ObiKwiet/Ultralight-Headset/Drawings/SCH1100-2 - IO Module r-.pdf

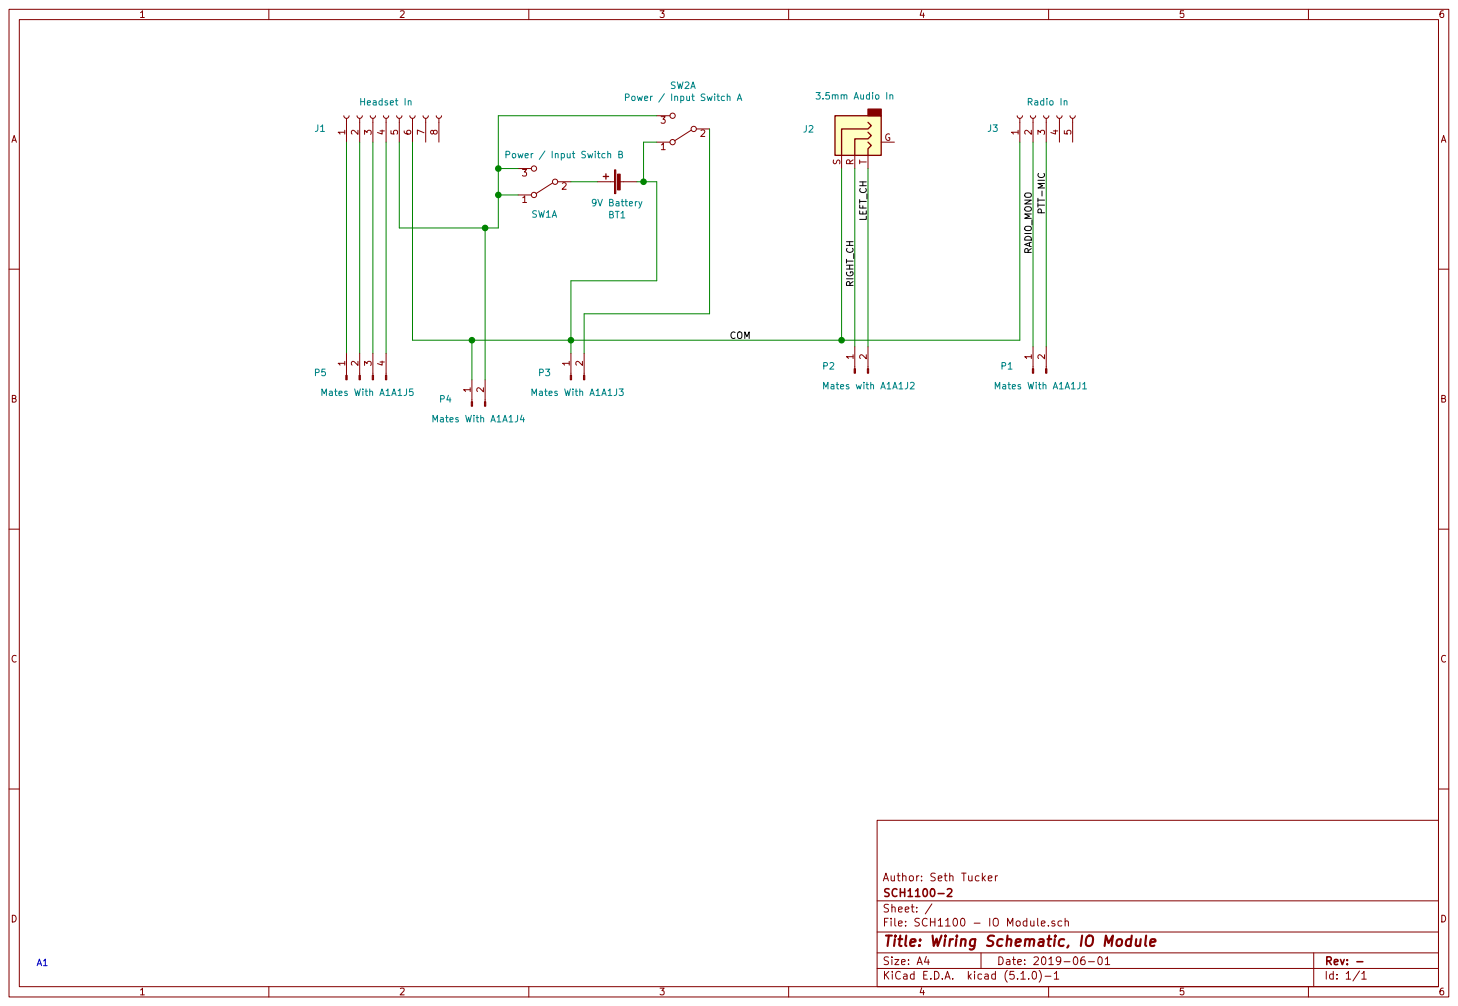
[picture p18: page 1]

Power / Input Switch A COM

File: SCH1100 - IO Module.sch Sheet: / SCH1100-2 Author: Seth Tucker

Id: 1/1 Title: Wiring Schematic, IO Module
