ObiKwiet/Ultralight-Headset/Drawings/SCH1110-2 - IO Module PCB r-.pdf

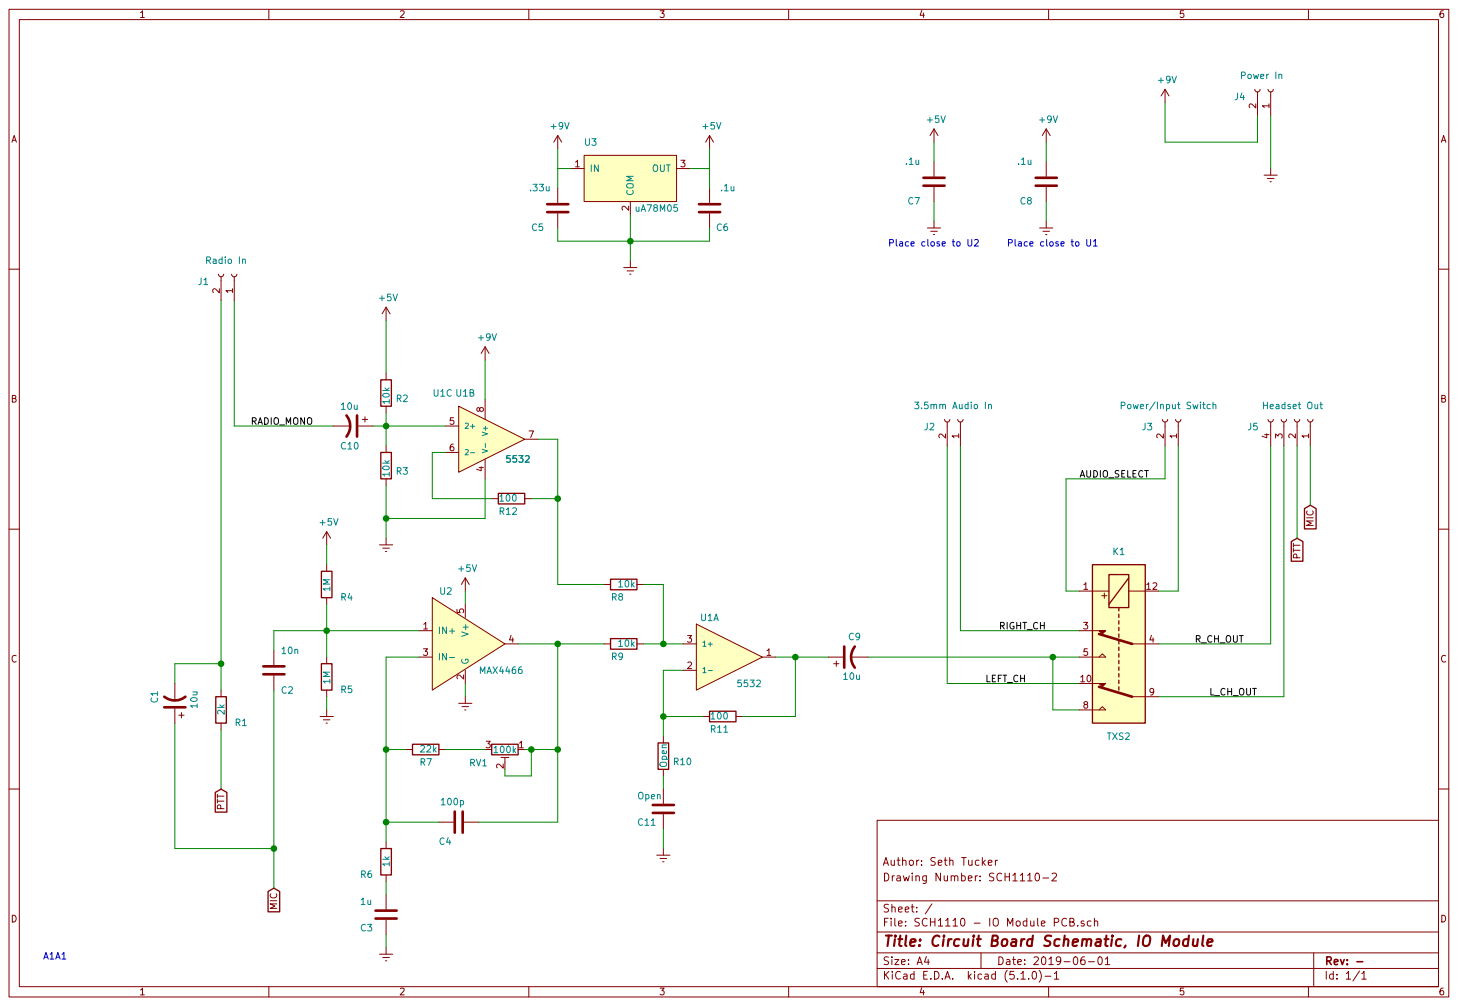
[picture p19: page 1]

Id: 1/1 Title: Circuit Board Schematic, IO Module
