ObiKwiet/Ultralight-Headset/Drawings/Drawing Tree.pdf

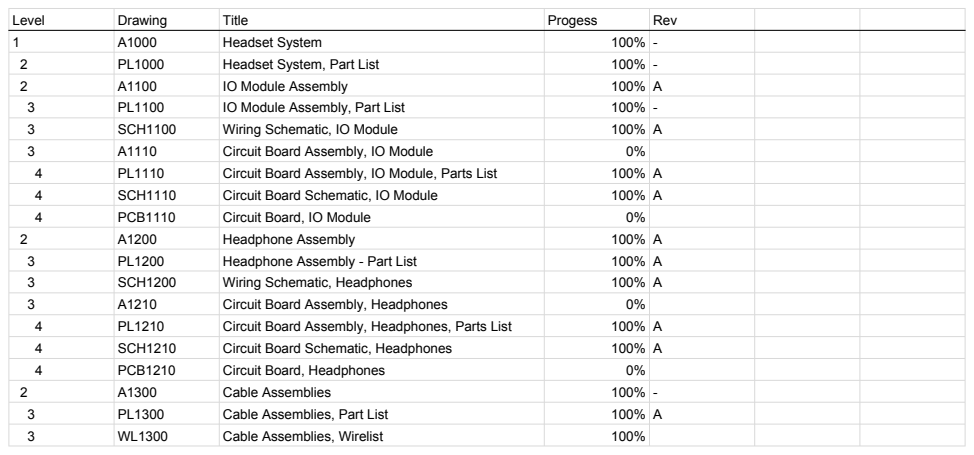
[picture p20: page 1]
Level; Drawing; Title; Progess; Rev; Headset System; Headset System, Part List; IO Module Assembly; IO Module Assembly, Part List; SCH1100; Wiring Schematic, IO Module; Circuit Board Assembly, IO Module; Circuit Board Assembly, IO Module, Parts List; SCH1110; Circuit Board Schematic, IO Module; PCB1110; Circuit Board, IO Module; Headphone Assembly; Headphone Assembly - Part List; SCH1200; Wiring Schematic, Headphones; Circuit Board Assembly, Headphones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
