ObiKwiet/Ultralight-Headset/KiCad/SCH1200 - Wiring Schematic, Headphones/SCH1200 - Wiring Schematic, Headphones - r-.pdf

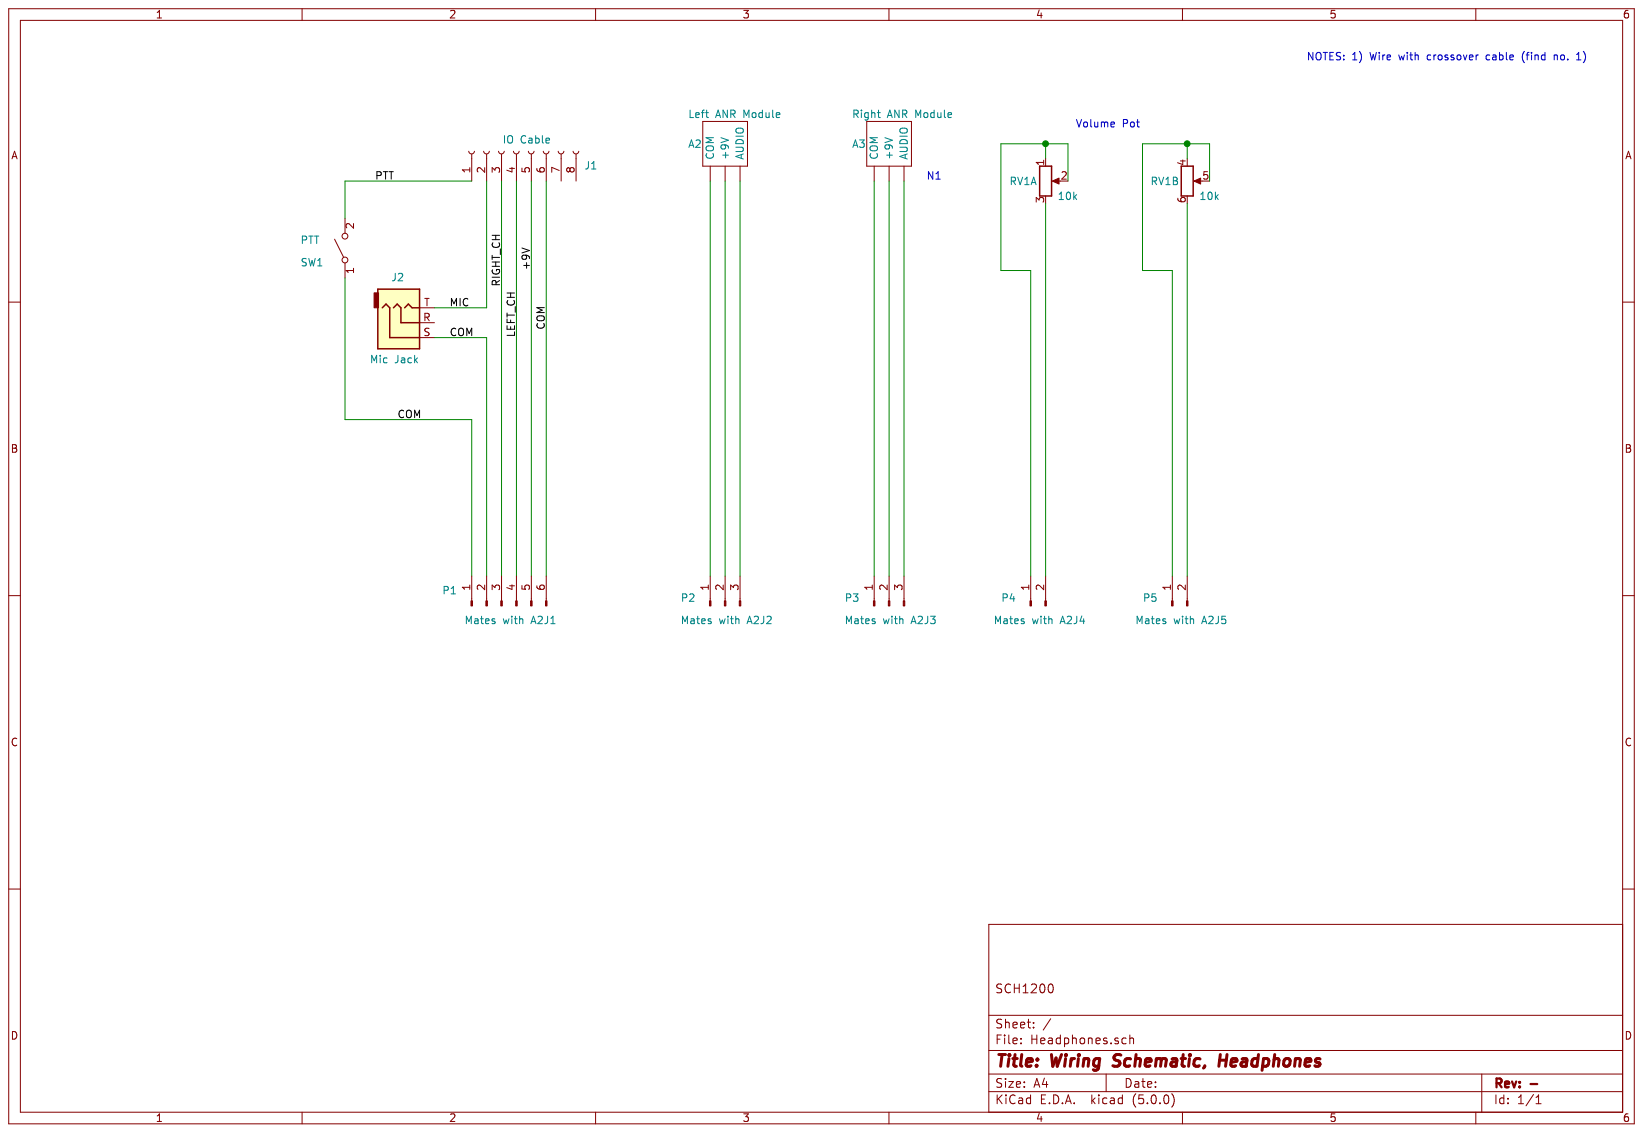
[picture p23: page 1]
