ObiKwiet/Ultralight-Headset/KiCad/SCH1210 - Circuit Board, Headphones/SCH1210 - Circuit Board, Headphones r-.pdf

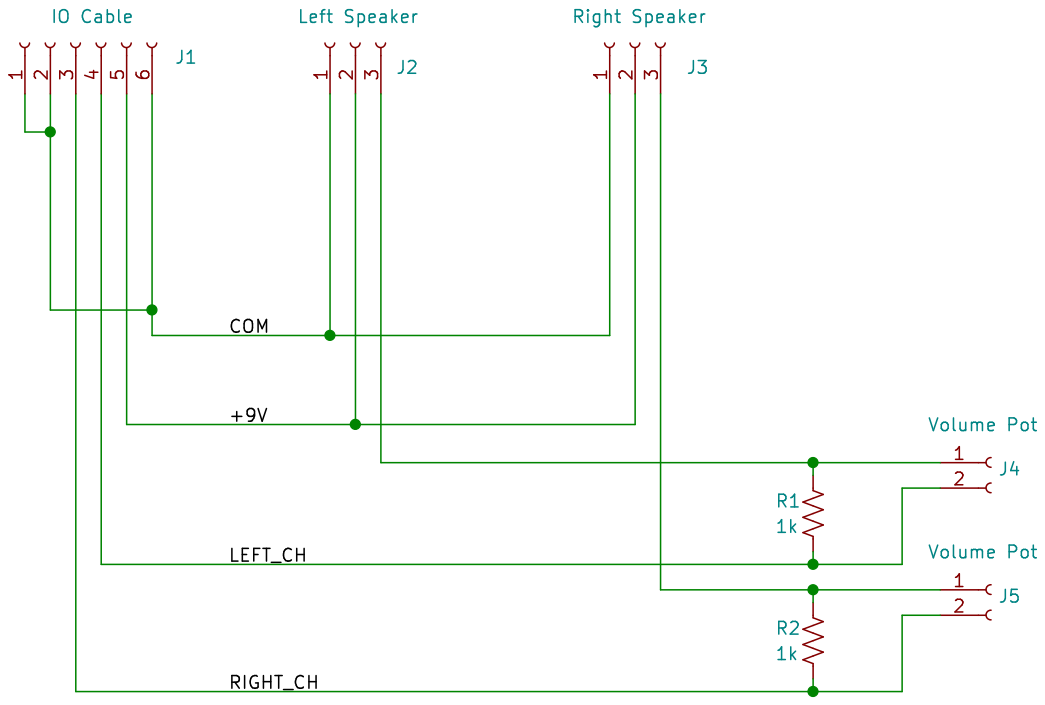
[picture p24: page 1]
