ObiKwiet/Ultralight-Headset/Drawings/Old Drawings/A1200 - Headphone Assembly - p-.pdf

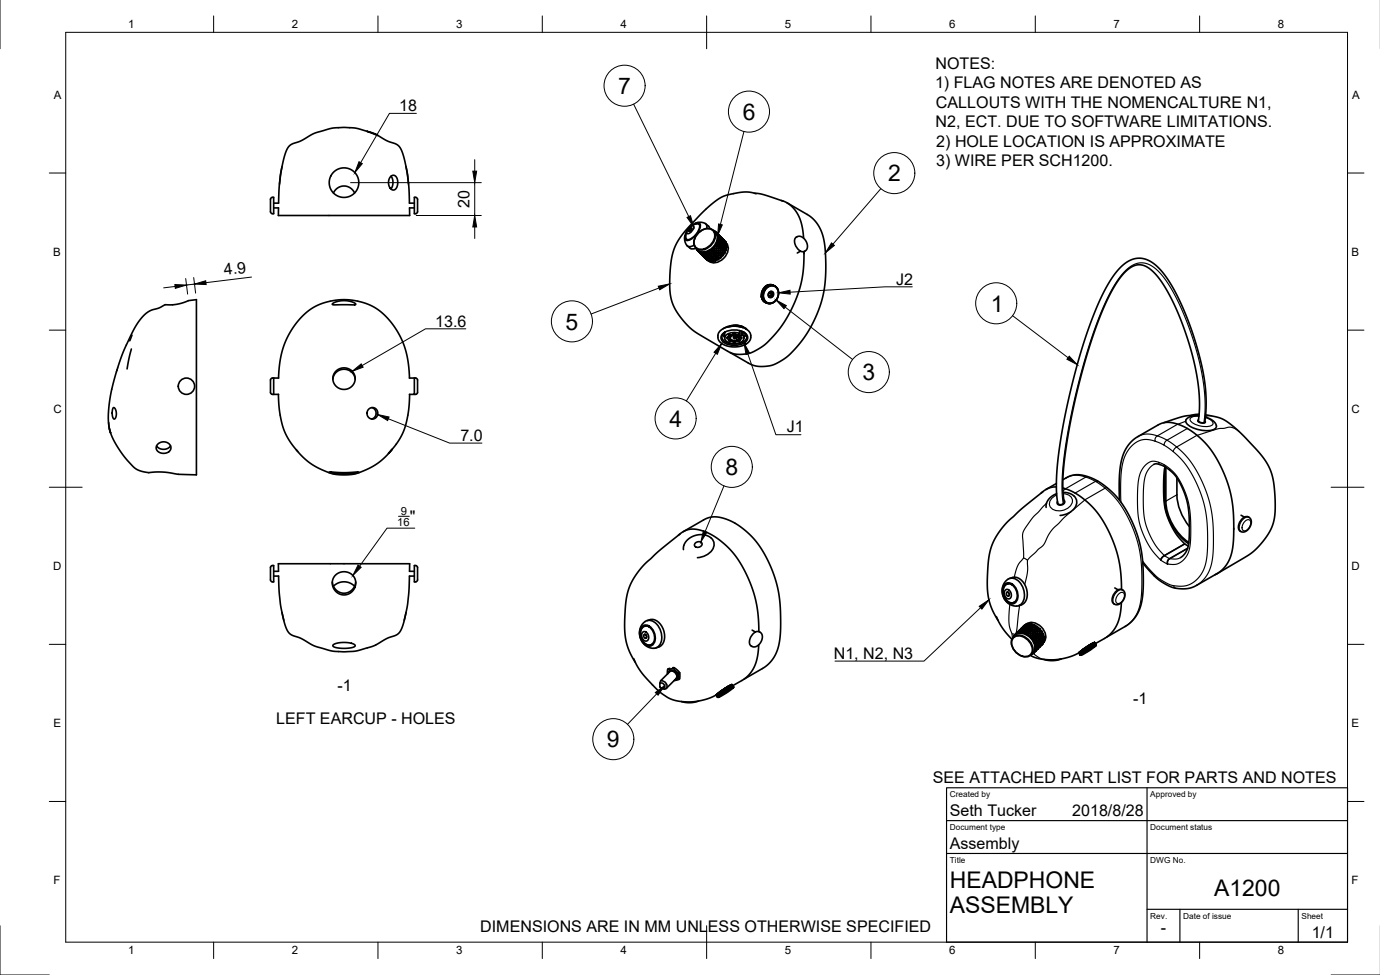
[picture p25: page 1]

NOTES:
1) FLAG NOTES ARE DENOTED AS
CALLOUTS WITH THE NOMENCALTURE N1,
N2, ECT. DUE TO SOFTWARE LIMITATIONS.
2) HOLE LOCATION IS APPROXIMATE
3) WIRE PER SCH1200.

LEFT EARCUP - HOLES

SEE ATTACHED PART LIST FOR PARTS AND NOTES

Created by Seth Tucker 2018/8/28 | Approved by

Document type | Document status
Title HEADPHONE ASSEMBLY | Rev. Date of issue Sheet - Assembly DWG No. A1200

DIMENSIONS ARE IN MM UNLESS OTHERWISE SPECIFIED

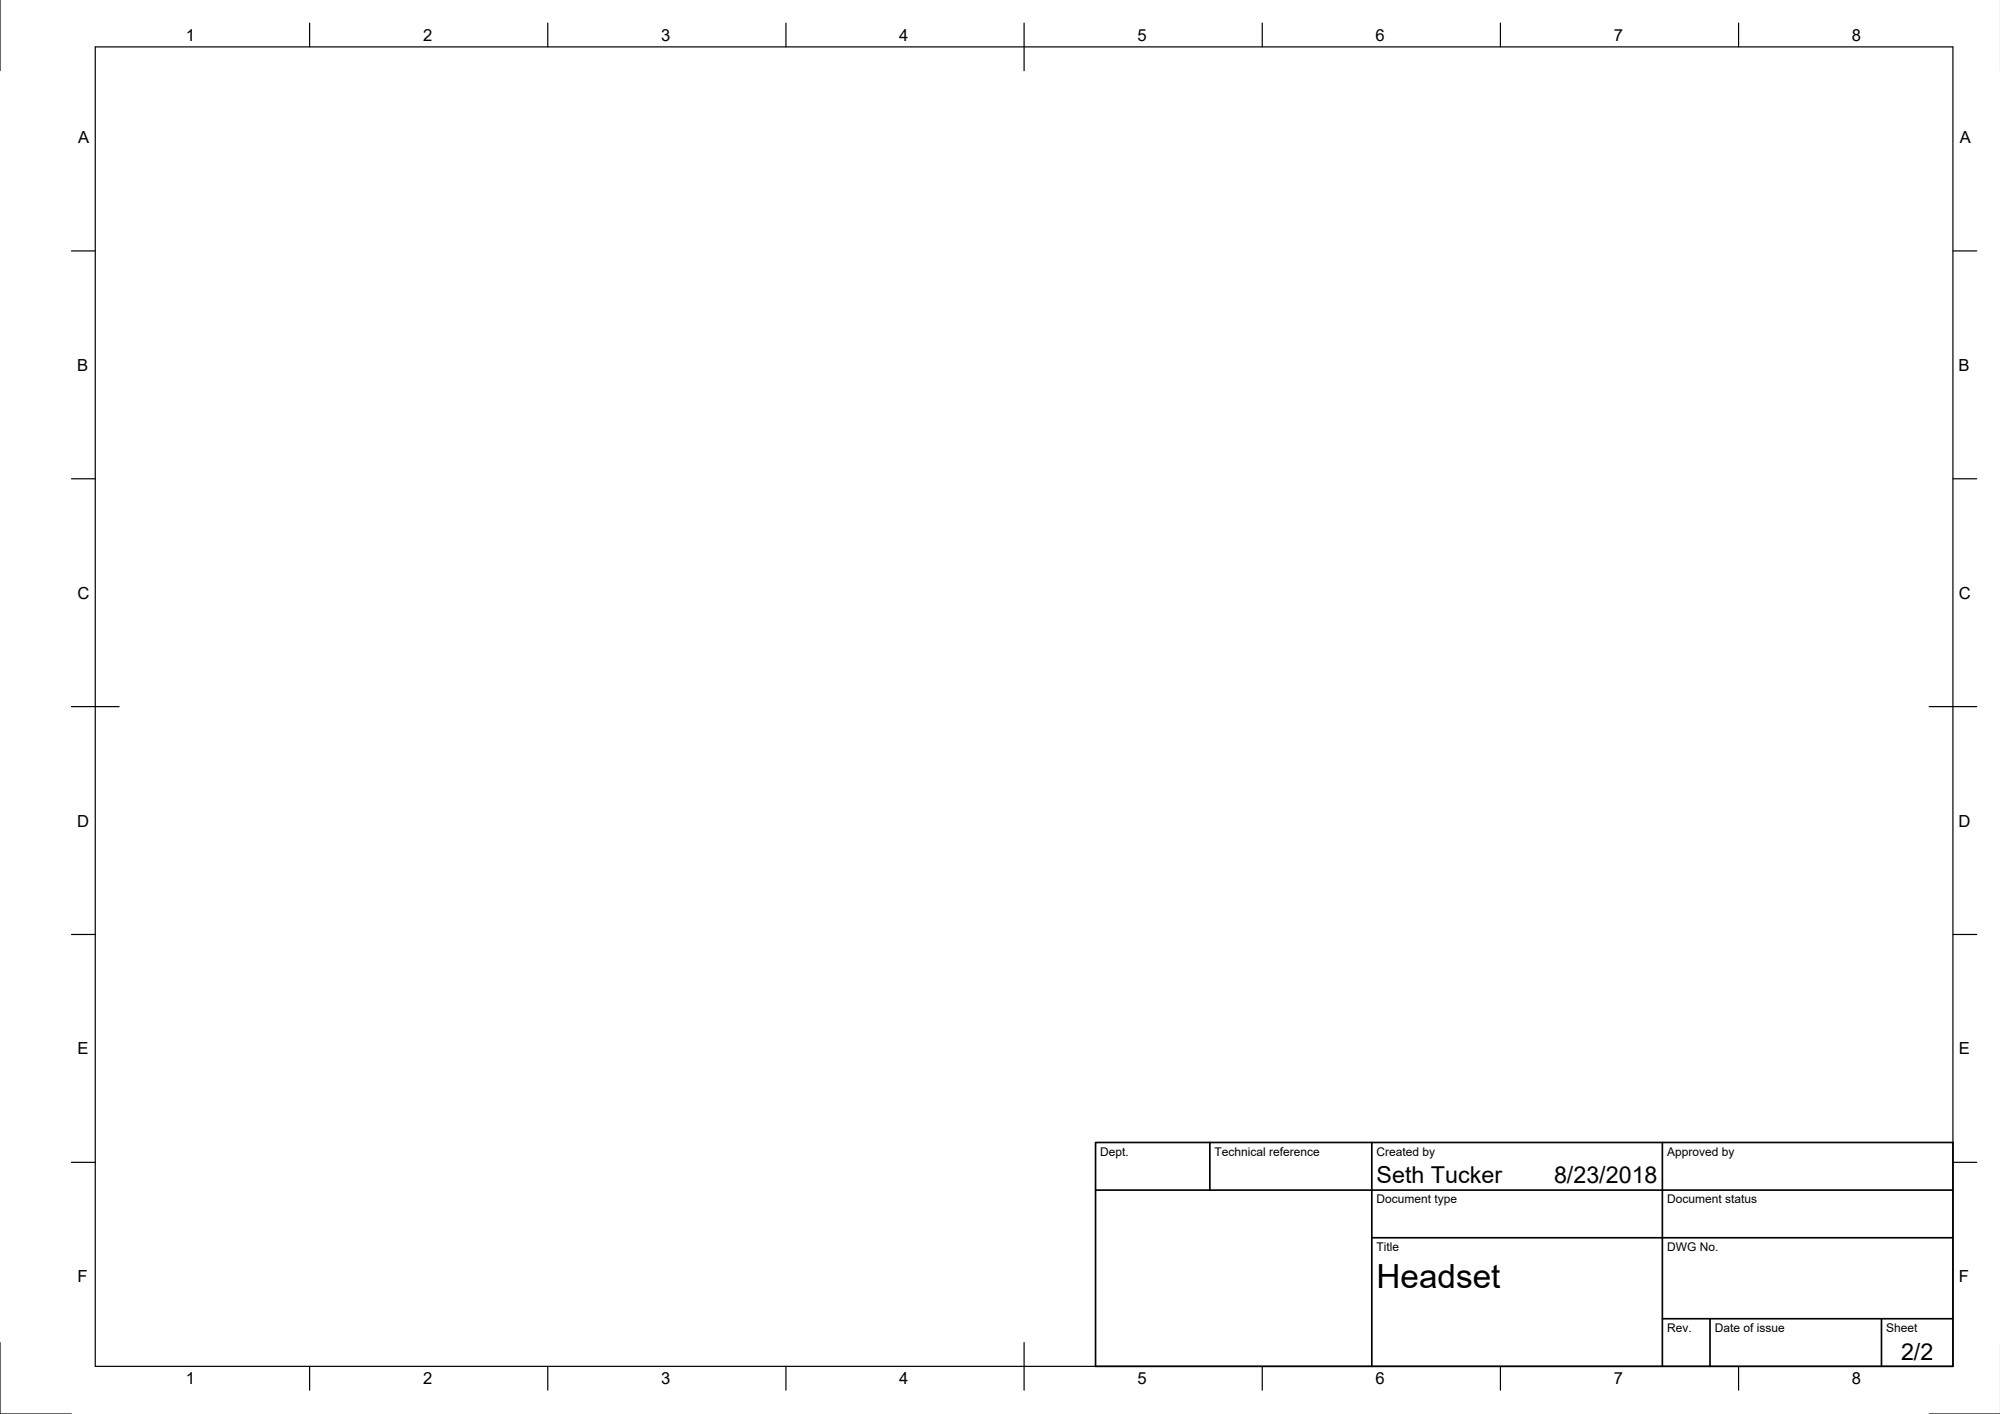
[picture p26: page 2]

Dept. | Technical reference | Created by Seth Tucker 8/23/2018 | Approved by

Document type | Document status

Title Headset | DWG No.

Rev. | Date of issue | Sheet 2/2
