ObiKwiet/Ultralight-Headset/Drawings/Old Drawings/PL1110 - Circuit Board Assembly, IO Module, Parts List p-.pdf

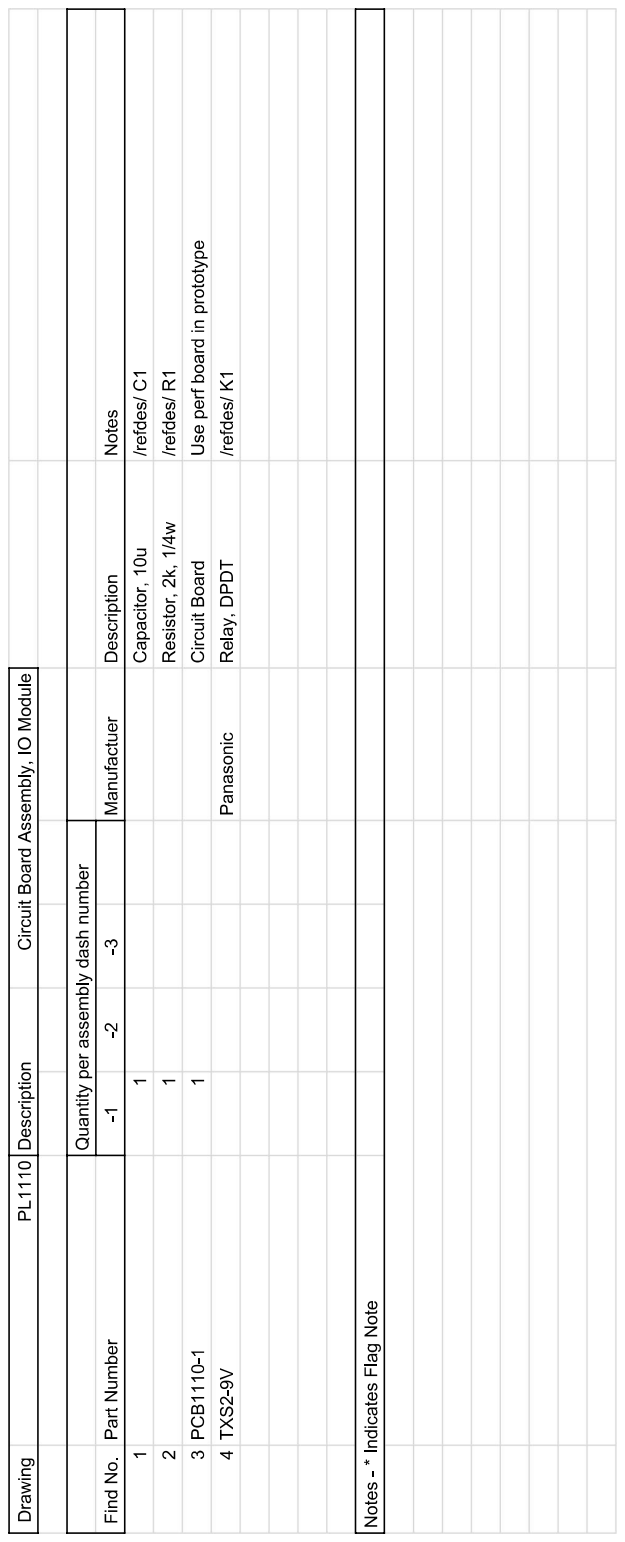
[picture p27: page 1]
