ObiKwiet/Ultralight-Headset/Drawings/Old Drawings/PL1200 - Headphone Assembly, Part List p-.pdf

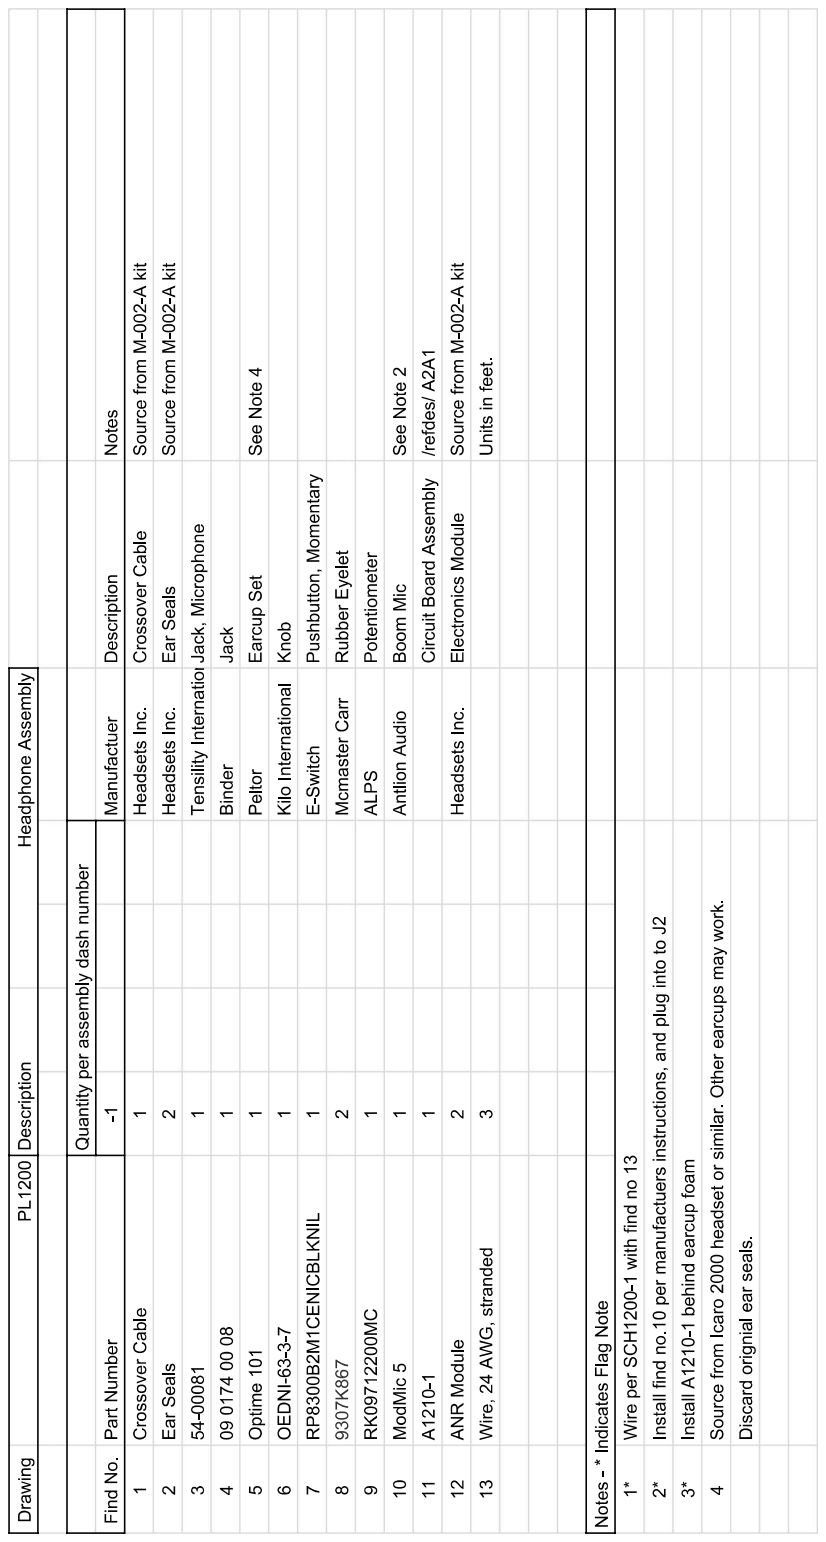
[picture p28: page 1]
