ObiKwiet/Ultralight-Headset/Drawings/Old Drawings/PL1210 - Circuit Board Assembly, Headphones, Parts List p-.pdf

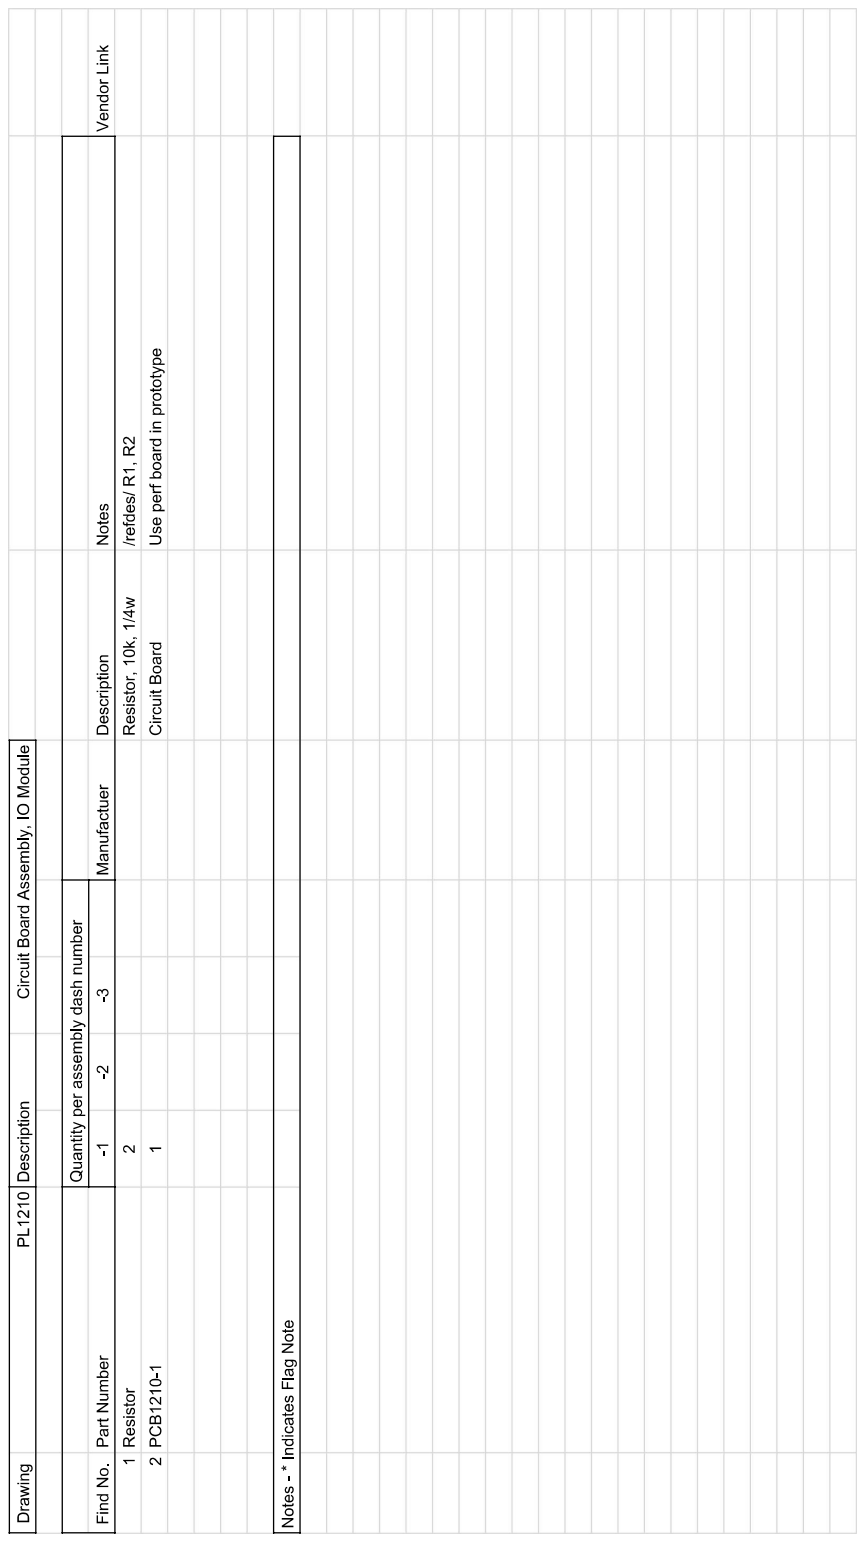
[picture p29: page 1]
