ObiKwiet/Ultralight-Headset/Drawings/Old Drawings/PL1300 - Cable Assemblies, Part List p-.pdf

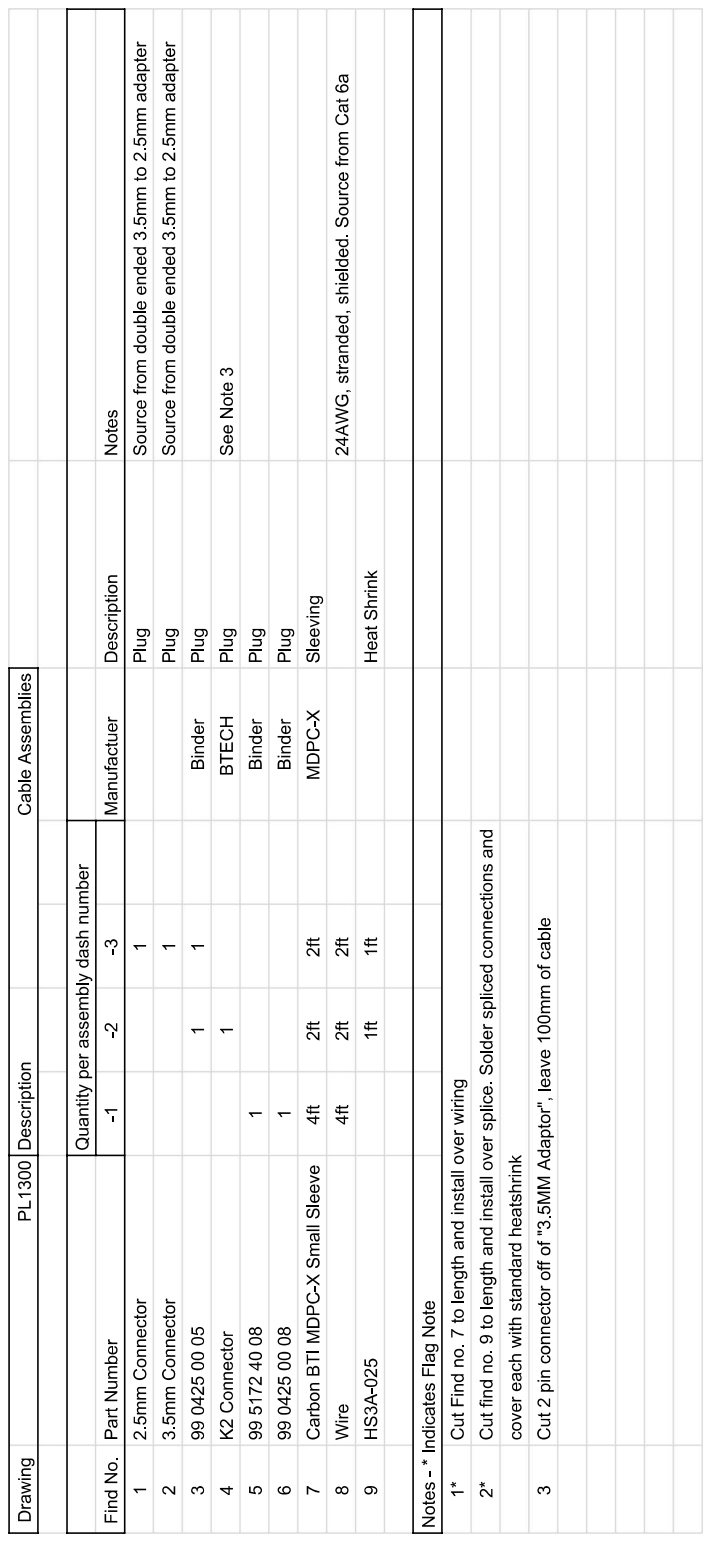
[picture p30: page 1]
