ObiKwiet/Ultralight-Headset/Drawings/Old Drawings/WL1300 - Cable Assemblies, Wirelist p-.pdf

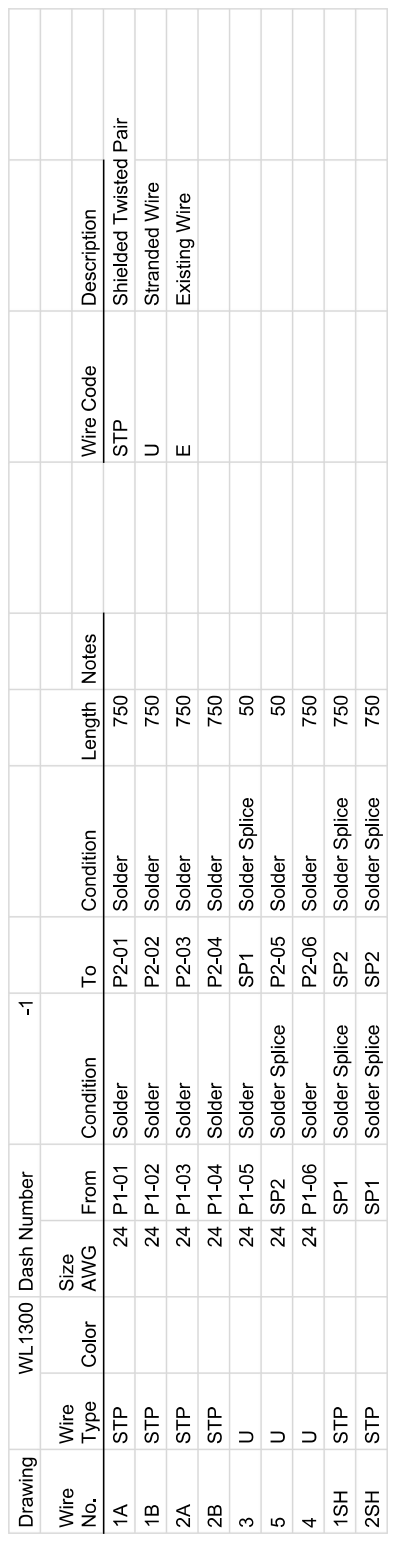
[picture p31: page 1]

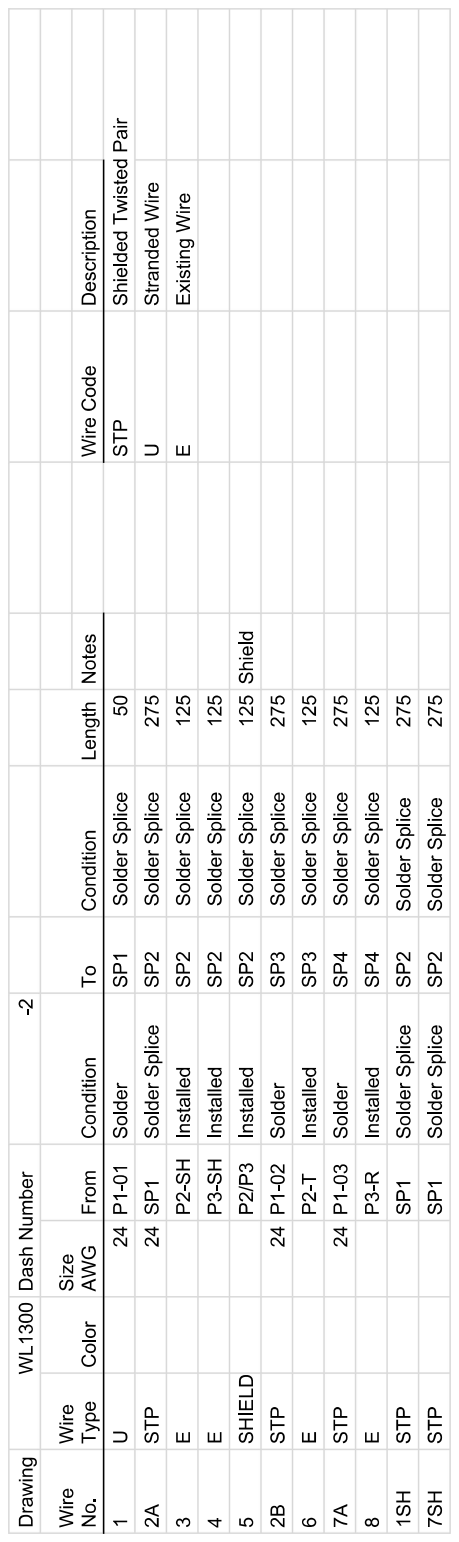
[picture p32: page 2]

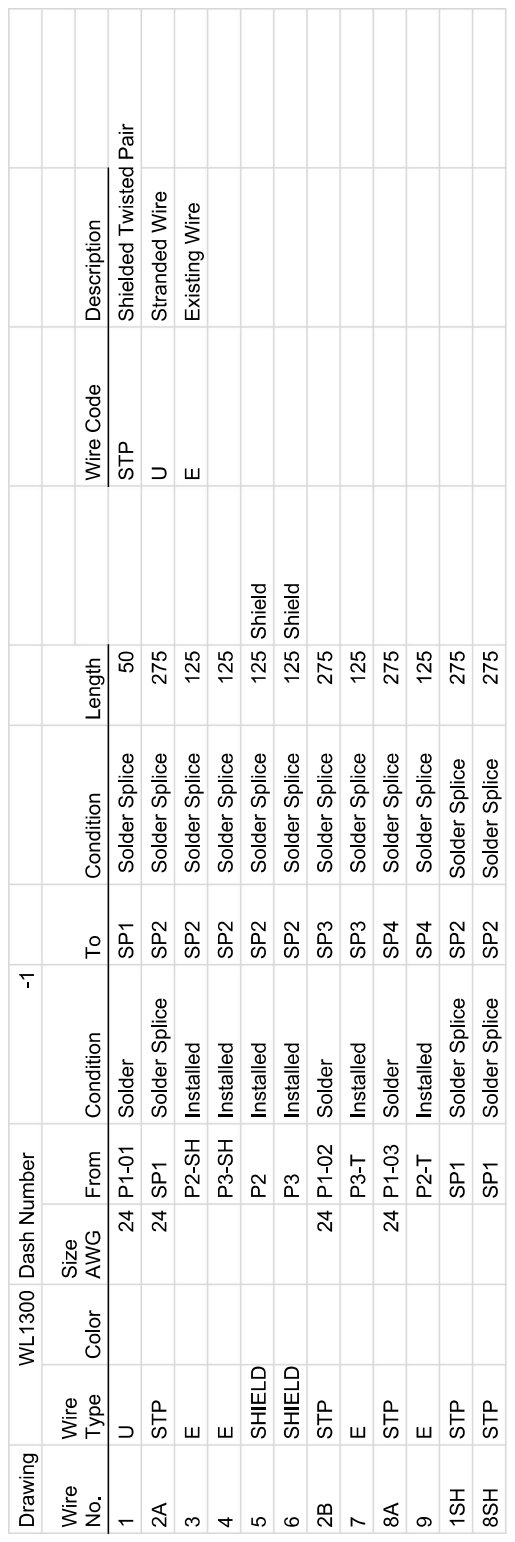
[picture p33: page 3]
